roblehmann/NinjaPBR/img/captor2.jpg

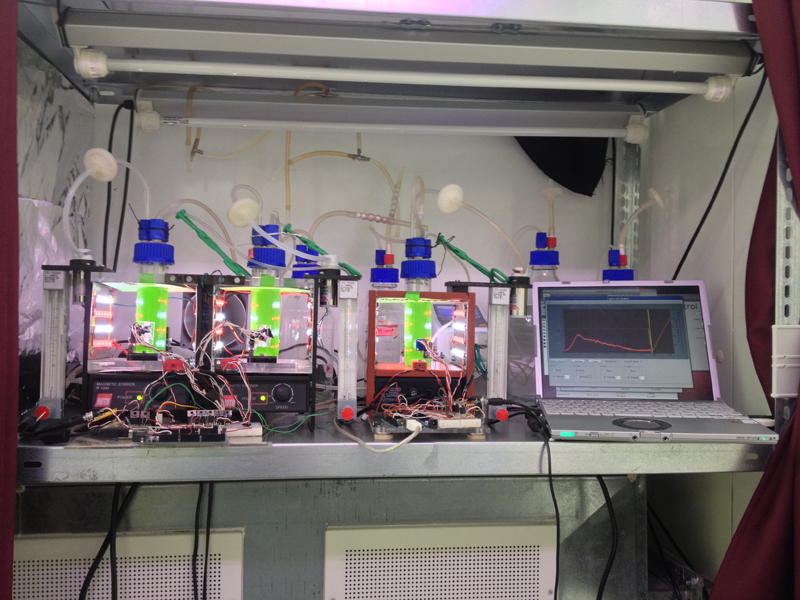
img/captor2.jpg
