roblehmann/NinjaPBR/img/captor.jpg

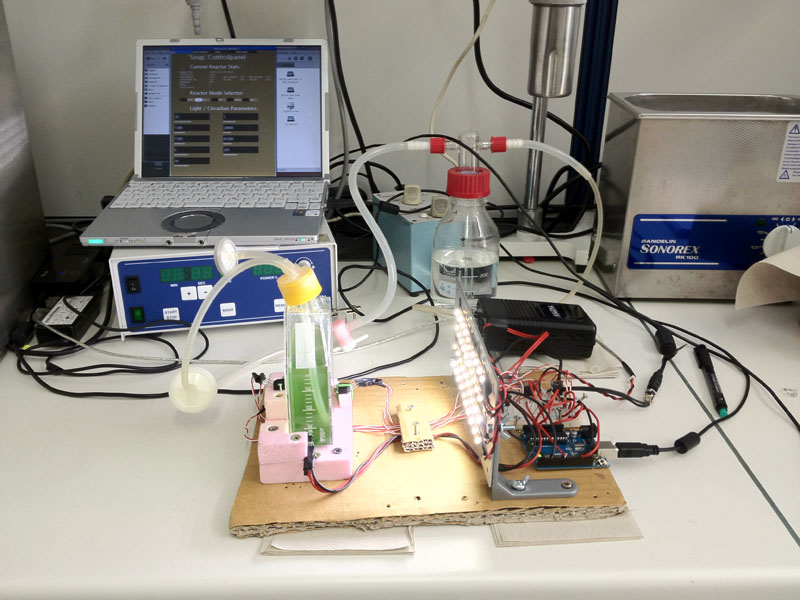
img/captor.jpg
