roblehmann/NinjaPBR/img/template.png

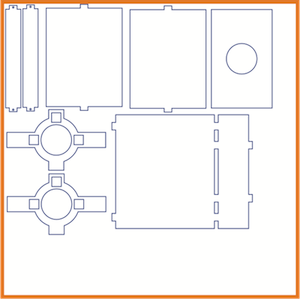
img/template.png
