roblehmann/NinjaPBR/img/wiki/controller/controller1.jpg

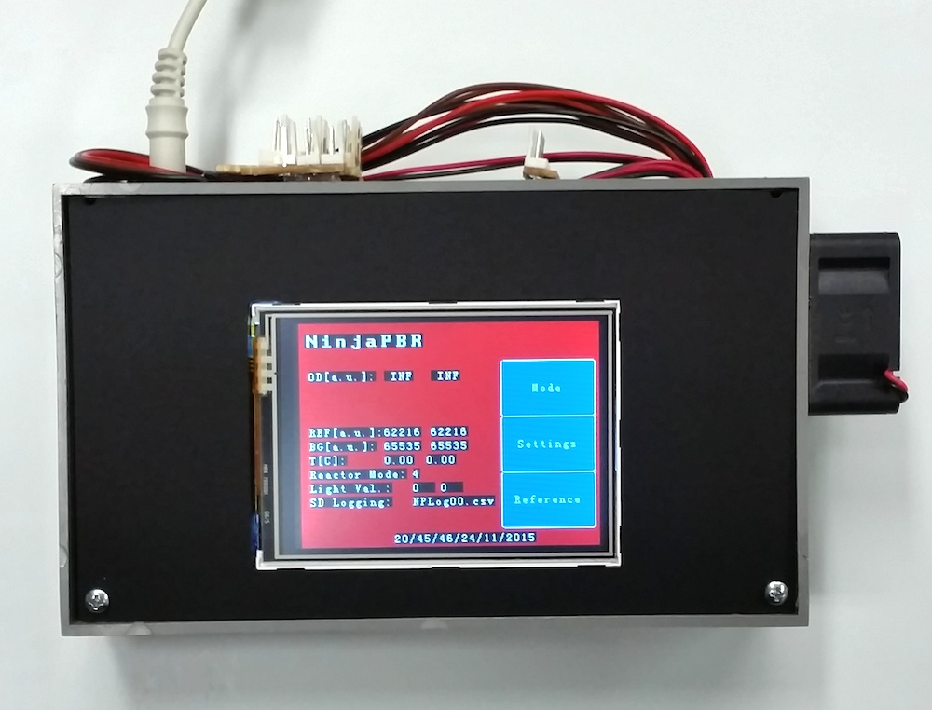
img/wiki/controller/controller1.jpg
