roblehmann/NinjaPBR/img/wiki/controller/controller2.jpg

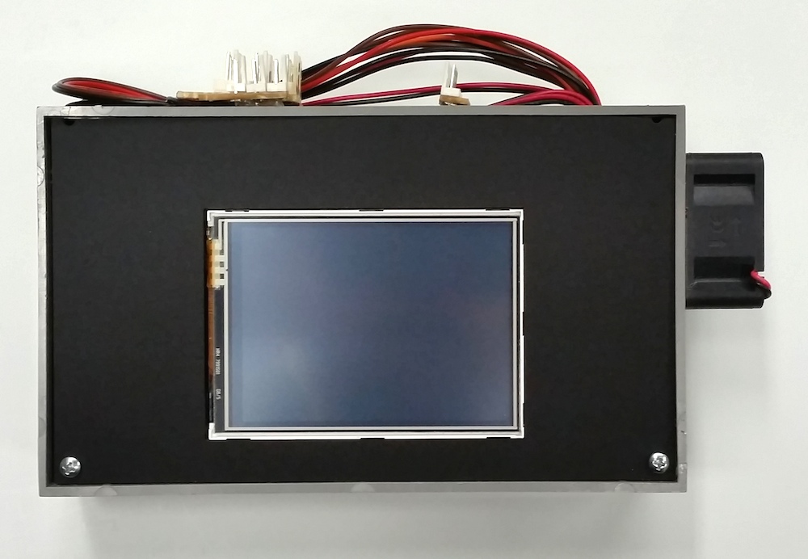
img/wiki/controller/controller2.jpg
