roblehmann/NinjaPBR/img/wiki/controller/controller4.jpg

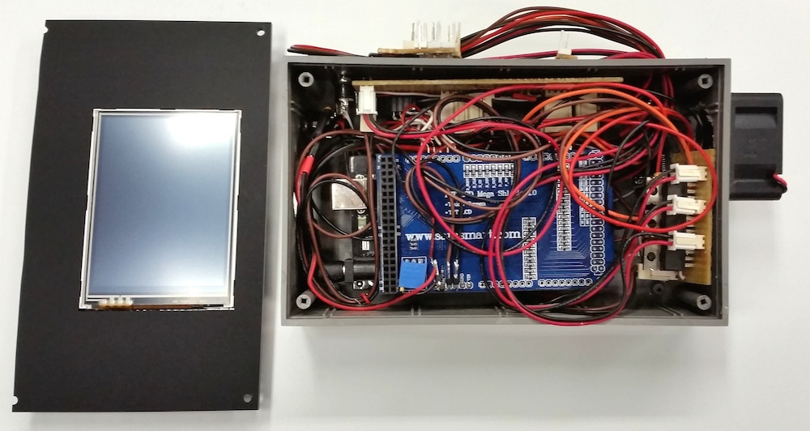
img/wiki/controller/controller4.jpg
