roblehmann/NinjaPBR/img/wiki/od/Buglabs_OD_vs_dilution.png

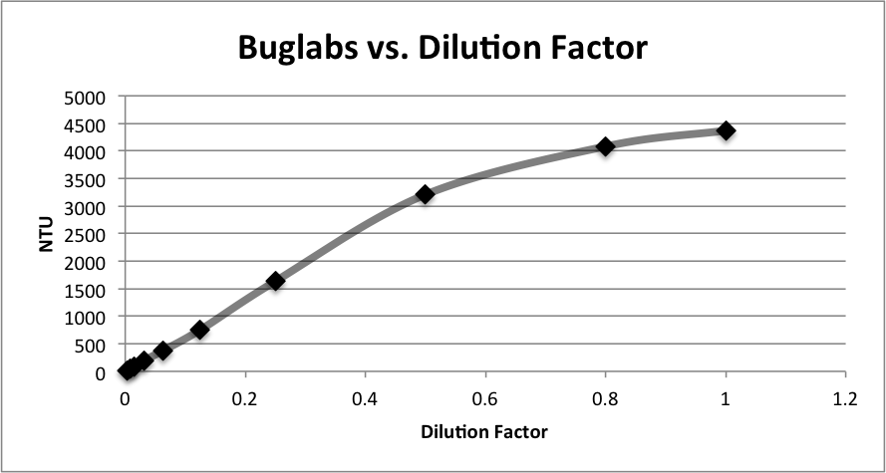
img/wiki/od/Buglabs_OD_vs_dilution.png
