roblehmann/NinjaPBR/img/wiki/od/NP_Buglabs.png

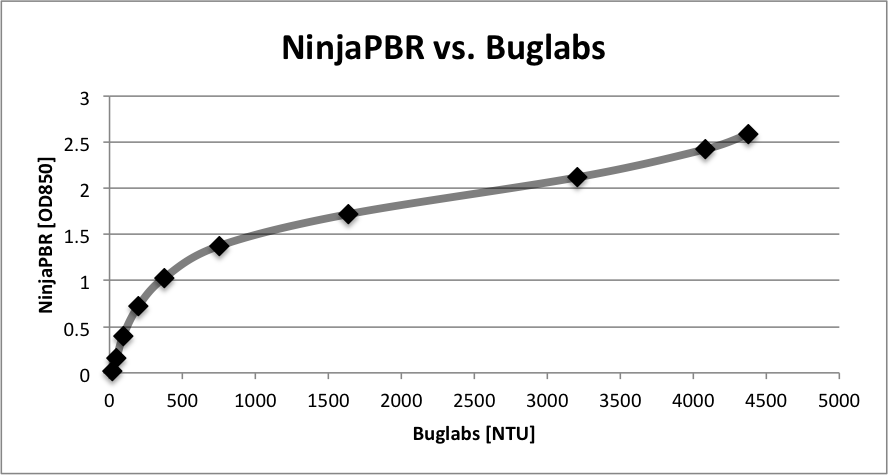
img/wiki/od/NP_Buglabs.png
