roblehmann/NinjaPBR/img/wiki/od/NP_Spekol_OD_vs_dilution.png

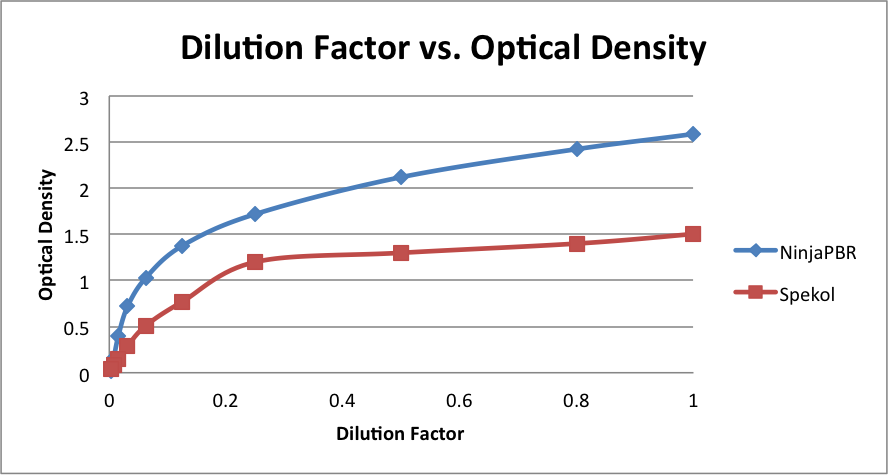
img/wiki/od/NP_Spekol_OD_vs_dilution.png
