roblehmann/NinjaPBR/img/wiki/od/ODschema.png

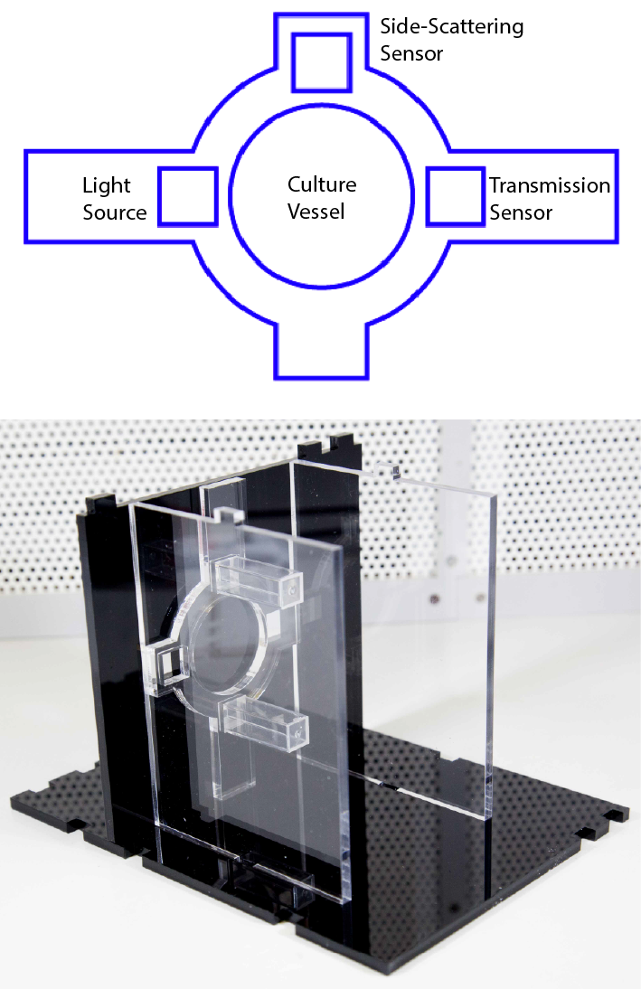
img/wiki/od/ODschema.png
