roblehmann/NinjaPBR/img/wiki/assembly/step1b.jpg

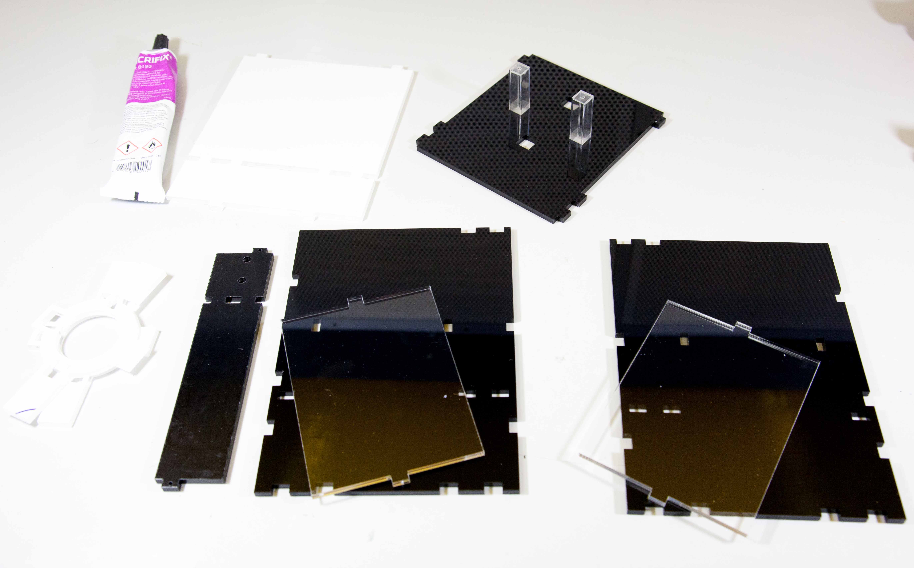
img/wiki/assembly/step1b.jpg
