roblehmann/NinjaPBR/img/wiki/assembly/step2.jpg

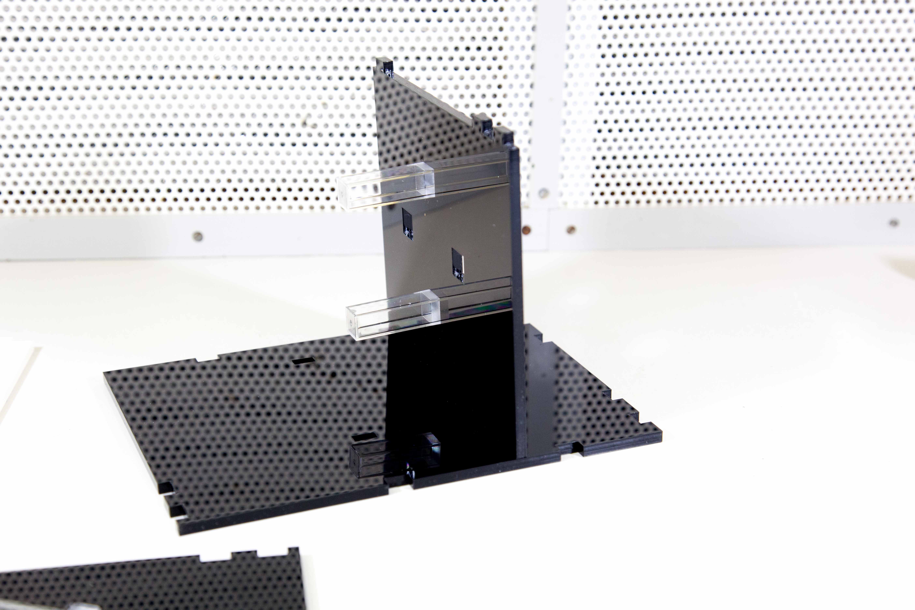
img/wiki/assembly/step2.jpg
