roblehmann/NinjaPBR/img/wiki/assembly/step3.jpg

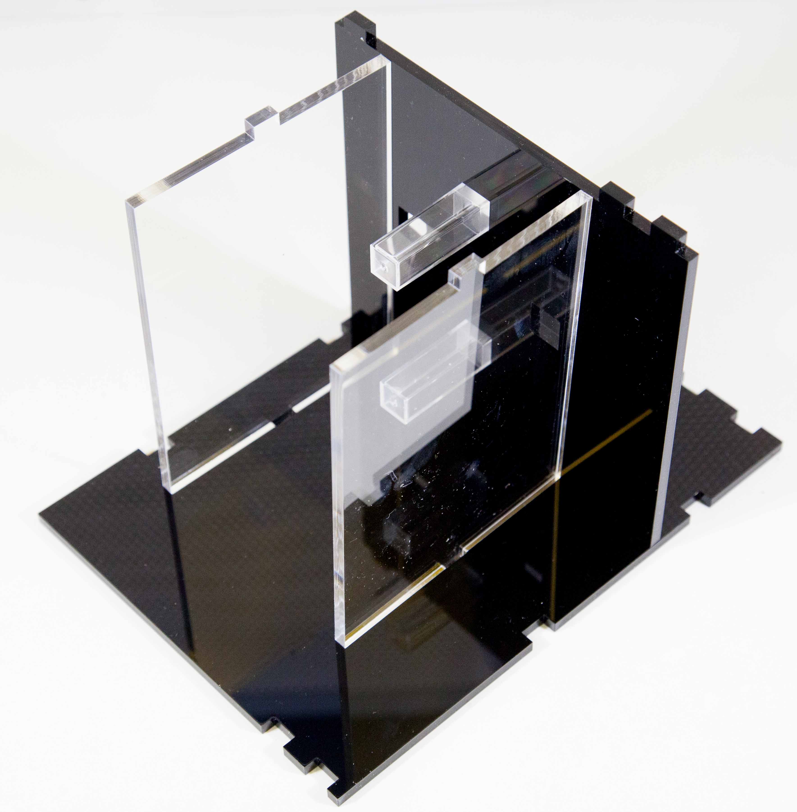
img/wiki/assembly/step3.jpg
