roblehmann/NinjaPBR/img/wiki/assembly/step4.jpg

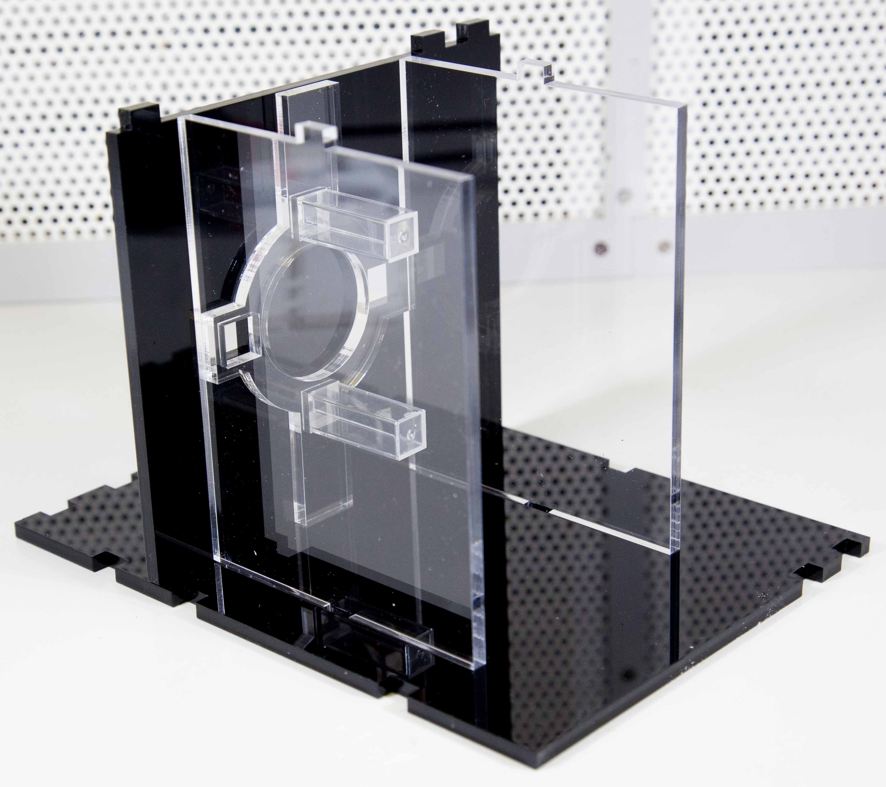
img/wiki/assembly/step4.jpg
